jcksnvllxr80/usb-controller-32/pcb/usb-controller-32/usb-controller-32.kicad_sch

## KiCad design pcb/usb-controller-32/usb-controller-32.kicad_sch (2026-04-13)

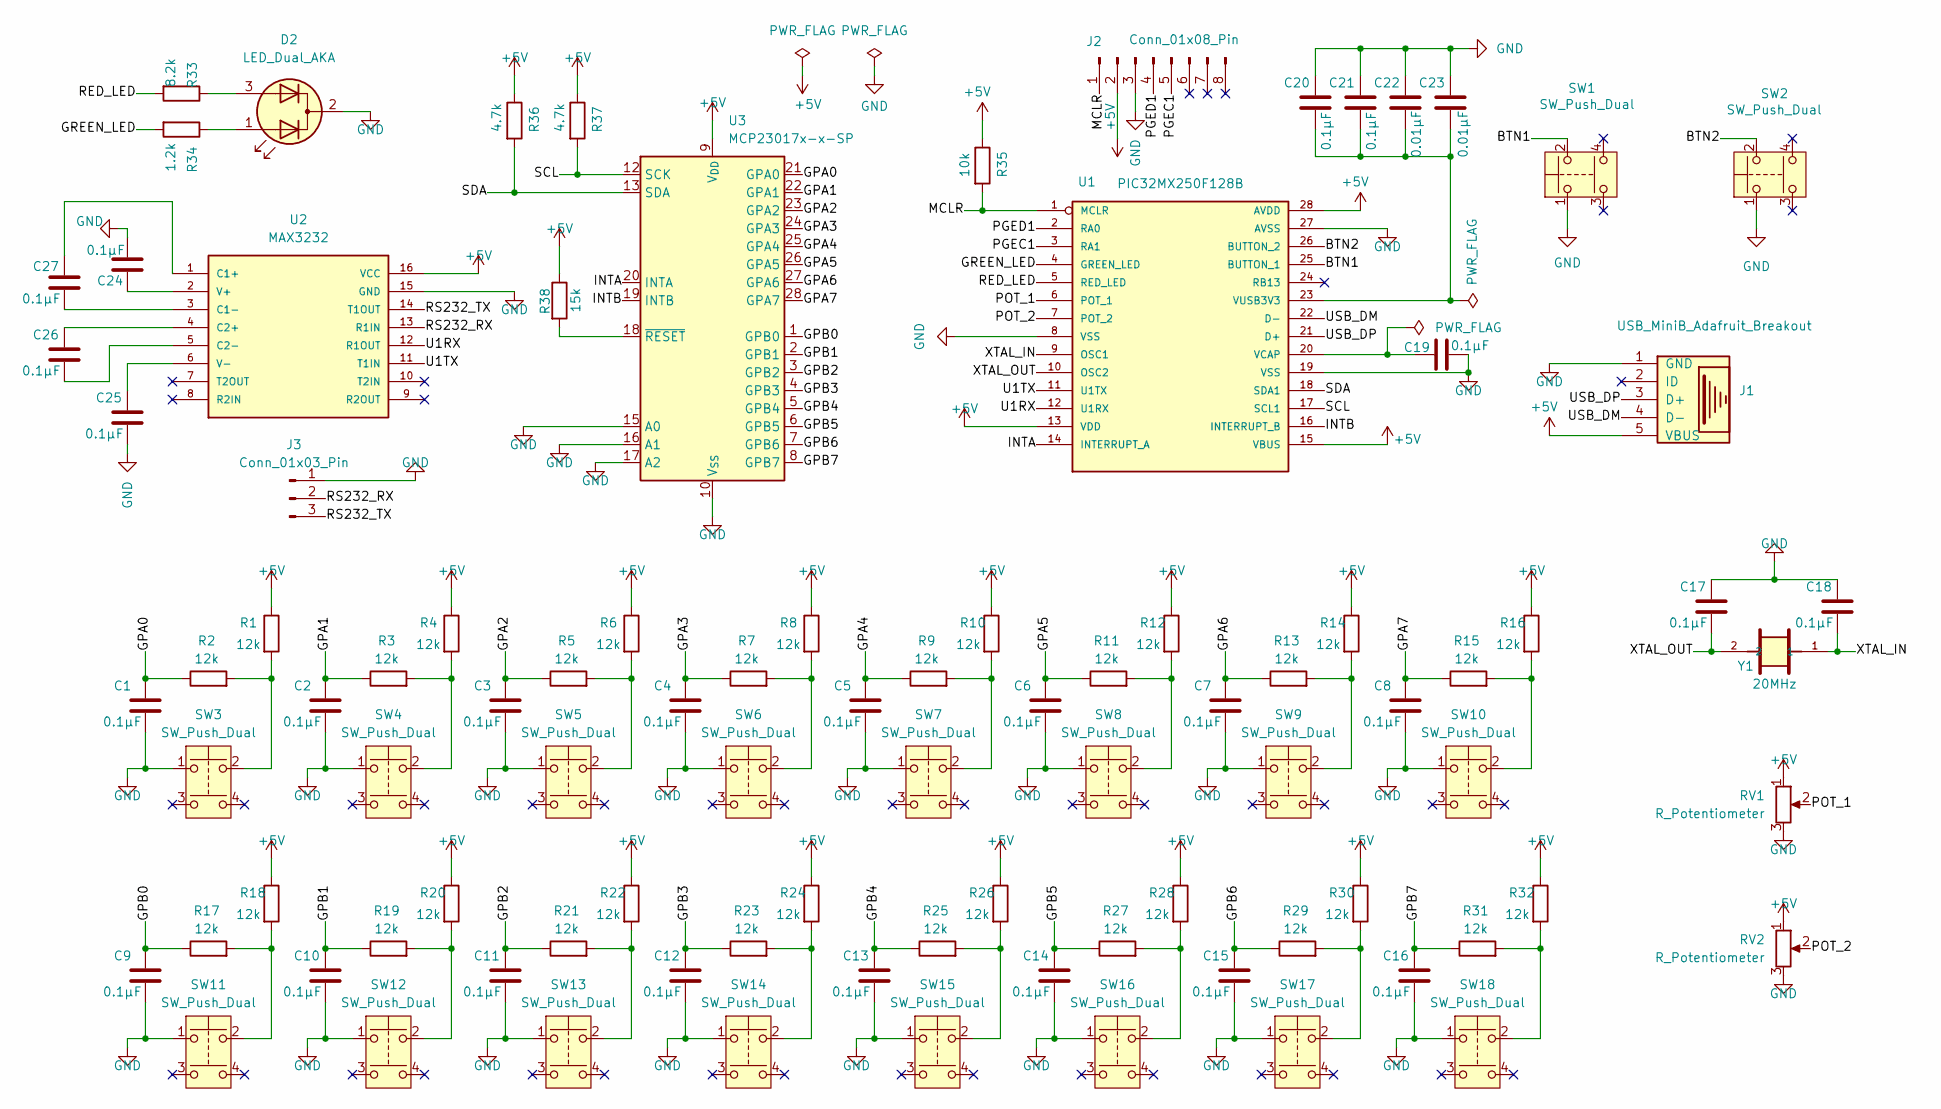
[picture p6: schematic usb-controller-32.kicad_sch]

Parts:
C1, C2, C3, C4, C5, C6, C7, C8, C9, C10, C11, C12, C13, C14, C15, C16, C17, C18, C19, C20, C21, C24, C25, C26, C27: 0.1µF; C_Disc_D5.0mm_W2.5mm_P2.50mm
C22, C23: 0.01µF; C_Disc_D5.0mm_W2.5mm_P2.50mm
D2: LED_Dual_AKA; LED_D3.0mm-3
J1: USB_MiniB_Adafruit_Breakout
J2: Conn_01x08_Pin; PinHeader_1x08_P2.54mm_Vertical
J3: Conn_01x03_Pin; PinHeader_1x03_P2.54mm_Vertical
R1, R2, R3, R4, R5, R6, R7, R8, R9, R10, R11, R12, R13, R14, R15, R16, R17, R18, R19, R20, R21, R22, R23, R24, R25, R26, R27, R28, R29, R30, R31, R32: 12k; R_Axial_DIN0207_L6.3mm_D2.5mm_P10.16mm_Horizontal
R33: 8.2k; R_Axial_DIN0207_L6.3mm_D2.5mm_P10.16mm_Horizontal
R34: 1.2k; R_Axial_DIN0207_L6.3mm_D2.5mm_P10.16mm_Horizontal
R35: 10k; R_Axial_DIN0207_L6.3mm_D2.5mm_P10.16mm_Horizontal
R36, R37: 4.7k; R_Axial_DIN0207_L6.3mm_D2.5mm_P10.16mm_Horizontal
R38: 15k; R_Axial_DIN0207_L6.3mm_D2.5mm_P10.16mm_Horizontal
RV1, RV2: R_Potentiometer; Potentiometer_Bourns_3386P_Vertical
SW1, SW2, SW3, SW4, SW5, SW6, SW7, SW8, SW9, SW10, SW11, SW12, SW13, SW14, SW15, SW16, SW17, SW18: SW_Push_Dual; SW_TH_Tactile_Omron_B3F-100x
U1: PIC32MX250F128B; DIP-28_W7.62mm
U2: MAX3232; DIP-16_W7.62mm
U3: MCP23017x-x-SP; DIP-28_W7.62mm
Y1: 20MHz; Crystal_HC49-4H_Vertical

Connections:
+5V: J1.5 (VBUS), J2.2, R1.1, R4.1, R6.1, R8.1, R10.1, R12.1, R14.1, R16.1, R18.1, R20.1, R22.1, R24.1, R26.1, R28.1, R30.1, R32.1, R35.1, R36.1, R37.1, R38.1, RV1.1, RV2.1, U1.13 (VDD), U1.15 (VBUS), U1.28 (AVDD), U2.16 (VCC), U3.9 (V_{DD})
BTN1: SW1.2, U1.25 (BUTTON_1)
BTN2: SW2.2, U1.26 (BUTTON_2)
GND: C1.1, C2.1, C3.1, C4.1, C5.1, C6.1, C7.1, C8.1, C9.1, C10.1, C11.1, C12.1, C13.1, C14.1, C15.1, C16.1, C17.2, C18.2, C19.1, C20.2, C21.2, C22.2, C23.2, C24.1, C25.1, D2.2 (K), J1.1 (GND), J2.3, J3.1, RV1.3, RV2.3, SW1.1, SW2.1, SW3.1, SW4.1, SW5.1, SW6.1, SW7.1, SW8.1, SW9.1, SW10.1, SW11.1, SW12.1, SW13.1, SW14.1, SW15.1, SW16.1, SW17.1, SW18.1, U1.8 (VSS), U1.19 (VSS), U1.27 (AVSS), U2.15 (GND), U3.10 (V_{SS}), U3.15 (A0), U3.16 (A1), U3.17 (A2)
GPA0: C1.2, R2.1, U3.21 (GPA0)
GPA1: C2.2, R3.1, U3.22 (GPA1)
GPA2: C3.2, R5.1, U3.23 (GPA2)
GPA3: C4.2, R7.1, U3.24 (GPA3)
GPA4: C5.2, R9.1, U3.25 (GPA4)
GPA5: C6.2, R11.1, U3.26 (GPA5)
GPA6: C7.2, R13.1, U3.27 (GPA6)
GPA7: C8.2, R15.1, U3.28 (GPA7)
GPB0: C9.2, R17.1, U3.1 (GPB0)
GPB1: C10.2, R19.1, U3.2 (GPB1)
GPB2: C11.2, R21.1, U3.3 (GPB2)
GPB3: C12.2, R23.1, U3.4 (GPB3)
GPB4: C13.2, R25.1, U3.5 (GPB4)
GPB5: C14.2, R27.1, U3.6 (GPB5)
GPB6: C15.2, R29.1, U3.7 (GPB6)
GPB7: C16.2, R31.1, U3.8 (GPB7)
GREEN_LED: R34.2, U1.4 (GREEN_LED)
INTA: U1.14 (INTERRUPT_A), U3.20 (INTA)
INTB: U1.16 (INTERRUPT_B), U3.19 (INTB)
MCLR: J2.1, R35.2, U1.1 (MCLR)
unnamed: C19.2, U1.20 (VCAP)
unnamed: C20.1, C21.1, C22.1, C23.1, U1.23 (VUSB3V3)
unnamed: C24.2, U2.2 (V+)
unnamed: C25.2, U2.6 (V-)
unnamed: C26.1, U2.5 (C2-)
unnamed: C26.2, U2.4 (C2+)
unnamed: C27.1, U2.3 (C1-)
unnamed: C27.2, U2.1 (C1+)
unnamed: D2.1 (A1), R34.1
unnamed: D2.3 (A2), R33.1
unnamed: R1.2, R2.2, SW3.2
unnamed: R3.2, R4.2, SW4.2
unnamed: R5.2, R6.2, SW5.2
unnamed: R7.2, R8.2, SW6.2
unnamed: R9.2, R10.2, SW7.2
unnamed: R11.2, R12.2, SW8.2
unnamed: R13.2, R14.2, SW9.2
unnamed: R15.2, R16.2, SW10.2
unnamed: R17.2, R18.2, SW11.2
unnamed: R19.2, R20.2, SW12.2
unnamed: R21.2, R22.2, SW13.2
unnamed: R23.2, R24.2, SW14.2
unnamed: R25.2, R26.2, SW15.2
unnamed: R27.2, R28.2, SW16.2
unnamed: R29.2, R30.2, SW17.2
unnamed: R31.2, R32.2, SW18.2
unnamed: R38.2, U3.18 (~RESET)
PGEC1: J2.5, U1.3 (RA1)
PGED1: J2.4, U1.2 (RA0)
POT_1: RV1.2, U1.6 (POT_1)
POT_2: RV2.2, U1.7 (POT_2)
RED_LED: R33.2, U1.5 (RED_LED)
RS232_RX: J3.2, U2.13 (R1IN)
RS232_TX: J3.3, U2.14 (T1OUT)
SCL: R37.2, U1.17 (SCL1), U3.12 (SCK)
SDA: R36.2, U1.18 (SDA1), U3.13 (SDA)
U1RX: U1.12 (U1RX), U2.12 (R1OUT)
U1TX: U1.11 (U1TX), U2.11 (T1IN)
USB_DM: J1.4 (D-), U1.22 (D-)
USB_DP: J1.3 (D+), U1.21 (D+)
XTAL_IN: C18.1, U1.9 (OSC1), Y1.1
XTAL_OUT: C17.1, U1.10 (OSC2), Y1.2
