jcksnvllxr80/usb-controller-32/usb-controller-32/src/mcp23017.cpp

#include "mcp23017.h"
#include "logger.h"

MCP23017::MCP23017(uint16_t address)
    : address_(address)
    , i2cDone_(false)
    , bankA_(0)
    , bankB_(0)
{
    txBuf_[0] = 0;
    txBuf_[1] = 0;
    rxBuf_[0] = 0;
}

void MCP23017::i2cCallback(uintptr_t context) {
    auto* flag = reinterpret_cast<volatile bool*>(context);
    *flag = true;
}

bool MCP23017::waitForI2C() {
    uint32_t timeout = 500000;
    while (!i2cDone_ && timeout > 0) {
        timeout--;
    }
    i2cDone_ = false;

    if (timeout == 0) {
        Logger::getInstance().log("MCP23017", "I2C timeout");
        return false;
    }
    if (I2C1_ErrorGet() != I2C_ERROR_NONE) {
        Logger::getInstance().log("MCP23017", "I2C error");
        return false;
    }
    return true;
}

bool MCP23017::writeRegister(Register reg, uint8_t value) {
    txBuf_[0] = static_cast<uint8_t>(reg);
    txBuf_[1] = value;

    if (!I2C1_Write(address_, txBuf_, 2)) {
        return false;
    }

    return waitForI2C();
}

bool MCP23017::readRegister(Register reg, uint8_t& value) {
    txBuf_[0] = static_cast<uint8_t>(reg);

    if (!I2C1_WriteRead(address_, txBuf_, 1, rxBuf_, 1)) {
        return false;
    }

    bool ok = waitForI2C();
    if (ok) {
        value = rxBuf_[0];
    }
    return ok;
}

bool MCP23017::readPortA(uint8_t& value) {
    return readRegister(GPIOA, value);
}

bool MCP23017::readPortB(uint8_t& value) {
    return readRegister(GPIOB, value);
}

bool MCP23017::init() {
    I2C1_CallbackRegister(i2cCallback, reinterpret_cast<uintptr_t>(&i2cDone_));

    Logger::getInstance().log("MCP23017", "Initializing...");

    // IOCON: BANK=0, MIRROR=0, SEQOP=0, INTPOL=0 (active-low), ODR=0
    if (!writeRegister(IOCON, 0x00)) return false;

    // All pins as inputs
    if (!writeRegister(IODIRA, 0xFF)) return false;
    if (!writeRegister(IODIRB, 0xFF)) return false;

    // Enable internal pull-ups on all pins
    if (!writeRegister(GPPUA, 0xFF)) return false;
    if (!writeRegister(GPPUB, 0xFF)) return false;

    // Non-inverted input polarity
    if (!writeRegister(IPOLA, 0x00)) return false;
    if (!writeRegister(IPOLB, 0x00)) return false;

    // Interrupt-on-change for all pins
    if (!writeRegister(GPINTENA, 0xFF)) return false;
    if (!writeRegister(GPINTENB, 0xFF)) return false;

    // Compare against previous pin value (not DEFVAL)
    if (!writeRegister(INTCONA, 0x00)) return false;
    if (!writeRegister(INTCONB, 0x00)) return false;

    // Read GPIO ports to clear any pending interrupts
    uint8_t dummy;
    (void)readRegister(GPIOA, dummy);
    (void)readRegister(GPIOB, dummy);
    bankA_ = 0;
    bankB_ = 0;

    Logger::getInstance().log("MCP23017", "Initialized successfully");
    return true;
}

bool MCP23017::handleInterruptA() {
    if (INTERRUPT_A_Get() != 0) return false;

    uint8_t flags = 0;
    uint8_t capture = 0;

    if (!readRegister(INTFA, flags) || !readRegister(INTCAPA, capture)) return false;

    capture = ~capture;  // pins are active low

    auto& logger = Logger::getInstance();

    // Pin 0
    if (flags & (1u << 0)) {
        if (capture & (1u << 0)) {
            bankA_ |= (1u << 0);
            logger.log("MCP23017", "Port A pin 0 HIGH");
        } else {
            bankA_ &= ~(1u << 0);
            logger.log("MCP23017", "Port A pin 0 LOW");
        }
    }
    // Pin 1
    if (flags & (1u << 1)) {
        if (capture & (1u << 1)) { bankA_ |= (1u << 1);  logger.log("MCP23017", "Port A pin 1 HIGH"); /* TODO */ }
        else                     { bankA_ &= ~(1u << 1); logger.log("MCP23017", "Port A pin 1 LOW");  /* TODO */ }
    }
    // Pin 2
    if (flags & (1u << 2)) {
        if (capture & (1u << 2)) { bankA_ |= (1u << 2);  logger.log("MCP23017", "Port A pin 2 HIGH"); /* TODO */ }
        else                     { bankA_ &= ~(1u << 2); logger.log("MCP23017", "Port A pin 2 LOW");  /* TODO */ }
    }
    // Pin 3
    if (flags & (1u << 3)) {
        if (capture & (1u << 3)) { bankA_ |= (1u << 3);  logger.log("MCP23017", "Port A pin 3 HIGH"); /* TODO */ }
        else                     { bankA_ &= ~(1u << 3); logger.log("MCP23017", "Port A pin 3 LOW");  /* TODO */ }
    }
    // Pin 4
    if (flags & (1u << 4)) {
        if (capture & (1u << 4)) { bankA_ |= (1u << 4);  logger.log("MCP23017", "Port A pin 4 HIGH"); /* TODO */ }
        else                     { bankA_ &= ~(1u << 4); logger.log("MCP23017", "Port A pin 4 LOW");  /* TODO */ }
    }
    // Pin 5
    if (flags & (1u << 5)) {
        if (capture & (1u << 5)) { bankA_ |= (1u << 5);  logger.log("MCP23017", "Port A pin 5 HIGH"); /* TODO */ }
        else                     { bankA_ &= ~(1u << 5); logger.log("MCP23017", "Port A pin 5 LOW");  /* TODO */ }
    }
    // Pin 6
    if (flags & (1u << 6)) {
        if (capture & (1u << 6)) { bankA_ |= (1u << 6);  logger.log("MCP23017", "Port A pin 6 HIGH"); /* TODO */ }
        else                     { bankA_ &= ~(1u << 6); logger.log("MCP23017", "Port A pin 6 LOW");  /* TODO */ }
    }
    // Pin 7
    if (flags & (1u << 7)) {
        if (capture & (1u << 7)) { bankA_ |= (1u << 7);  logger.log("MCP23017", "Port A pin 7 HIGH"); /* TODO */ }
        else                     { bankA_ &= ~(1u << 7); logger.log("MCP23017", "Port A pin 7 LOW");  /* TODO */ }
    }

    if (bankA_ != 0u) { GREEN_LED_Set(); } else { GREEN_LED_Clear(); }
    return true;
}

bool MCP23017::handleInterruptB() {
    if (INTERRUPT_B_Get() != 0) return false;

    uint8_t flags = 0;
    uint8_t capture = 0;

    if (!readRegister(INTFB, flags) || !readRegister(INTCAPB, capture)) return false;

    capture = ~capture;  // pins are active low

    auto& logger = Logger::getInstance();

    // Pin 0
    if (flags & (1u << 0)) {
        if (capture & (1u << 0)) {
            bankB_ |= (1u << 0);
            logger.log("MCP23017", "Port B pin 0 HIGH");
        }
        else {
            bankB_ &= ~(1u << 0);
            logger.log("MCP23017", "Port B pin 0 LOW");
        }
    }
    // Pin 1
    if (flags & (1u << 1)) {
        if (capture & (1u << 1)) { bankB_ |= (1u << 1);  logger.log("MCP23017", "Port B pin 1 HIGH"); /* TODO */ }
        else                     { bankB_ &= ~(1u << 1); logger.log("MCP23017", "Port B pin 1 LOW");  /* TODO */ }
    }
    // Pin 2
    if (flags & (1u << 2)) {
        if (capture & (1u << 2)) { bankB_ |= (1u << 2);  logger.log("MCP23017", "Port B pin 2 HIGH"); /* TODO */ }
        else                     { bankB_ &= ~(1u << 2); logger.log("MCP23017", "Port B pin 2 LOW");  /* TODO */ }
    }
    // Pin 3
    if (flags & (1u << 3)) {
        if (capture & (1u << 3)) { bankB_ |= (1u << 3);  logger.log("MCP23017", "Port B pin 3 HIGH"); /* TODO */ }
        else                     { bankB_ &= ~(1u << 3); logger.log("MCP23017", "Port B pin 3 LOW");  /* TODO */ }
    }
    // Pin 4
    if (flags & (1u << 4)) {
        if (capture & (1u << 4)) { bankB_ |= (1u << 4);  logger.log("MCP23017", "Port B pin 4 HIGH"); /* TODO */ }
        else                     { bankB_ &= ~(1u << 4); logger.log("MCP23017", "Port B pin 4 LOW");  /* TODO */ }
    }
    // Pin 5
    if (flags & (1u << 5)) {
        if (capture & (1u << 5)) { bankB_ |= (1u << 5);  logger.log("MCP23017", "Port B pin 5 HIGH"); /* TODO */ }
        else                     { bankB_ &= ~(1u << 5); logger.log("MCP23017", "Port B pin 5 LOW");  /* TODO */ }
    }
    // Pin 6
    if (flags & (1u << 6)) {
        if (capture & (1u << 6)) { bankB_ |= (1u << 6);  logger.log("MCP23017", "Port B pin 6 HIGH"); /* TODO */ }
        else                     { bankB_ &= ~(1u << 6); logger.log("MCP23017", "Port B pin 6 LOW");  /* TODO */ }
    }
    // Pin 7
    if (flags & (1u << 7)) {
        if (capture & (1u << 7)) { bankB_ |= (1u << 7);  logger.log("MCP23017", "Port B pin 7 HIGH"); /* TODO */ }
        else                     { bankB_ &= ~(1u << 7); logger.log("MCP23017", "Port B pin 7 LOW");  /* TODO */ }
    }

    if (bankB_ != 0u) { RED_LED_Set(); } else { RED_LED_Clear(); }
    return true;
}
